Andik2007/Cycling-computer/Bike Computer3.jpg

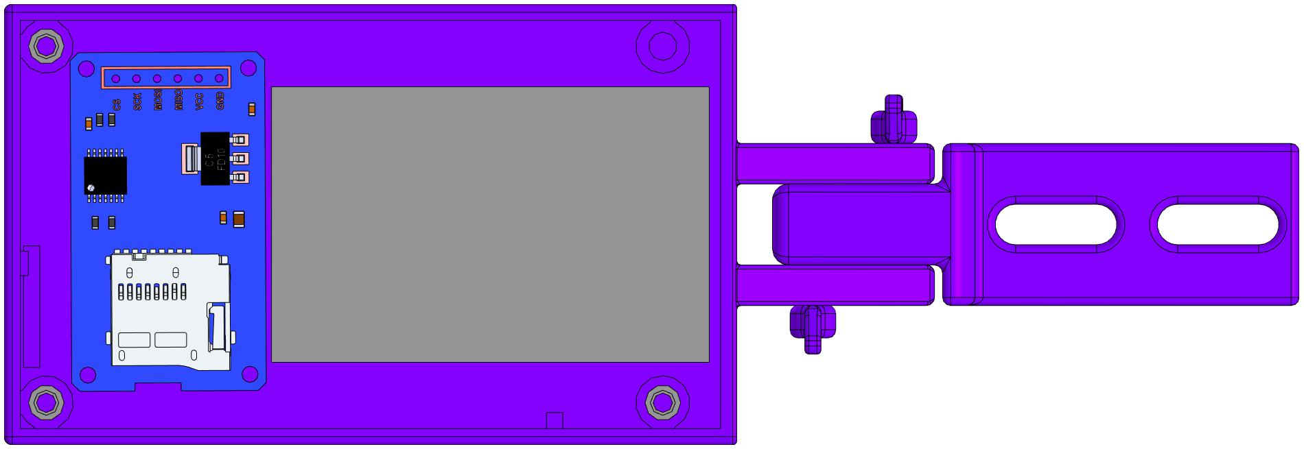
Bike Computer3.jpg
