Andik2007/Cycling-computer/Bike Computer.jpg

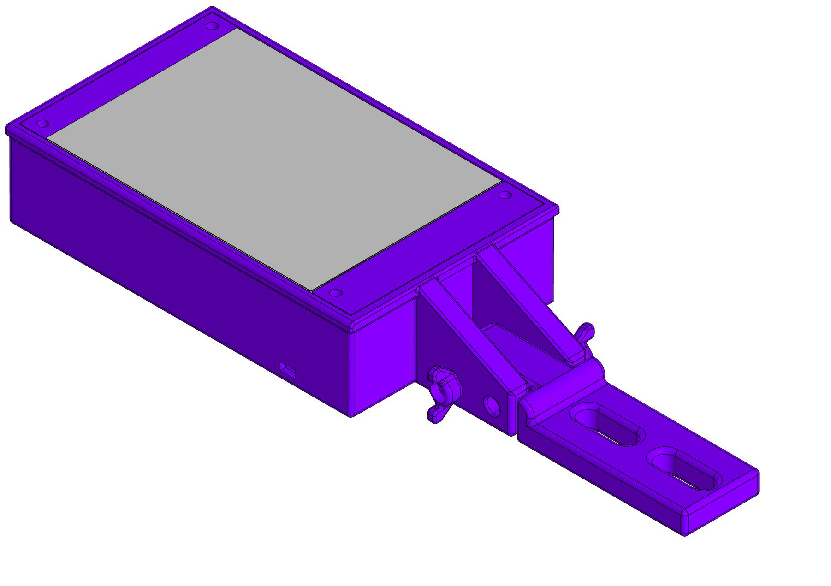
Bike Computer.jpg
